OG-netizen/Project-3-4/Sprint Planning/Scrum meeting 3.pptx

## PO Meeting

## Sprint review

- Nieuwe database
- Kleuren

## oude Presentatie Sprint Backlog

Features | Wat | Wie | Waarom | Taken | Moeilijkheids-graad | Acceptance criteria
4 | Bon laten printen. | De klant | Zodat je jouw transactie kan bekijken. | Fritzing van de bonprinter | 6 | De printer moet een bon kunnen printen met gekozen tekst
| | | | Code schrijven voor printer
5 | Kan zijn of haar saldo checken. | De klant | Zodat de klant overzicht heeft op zijn bank | Test database maken | 10 | De database moet een connectie hebben met de rest van de programma’s
| | | | Java > SQL

## Slide 4

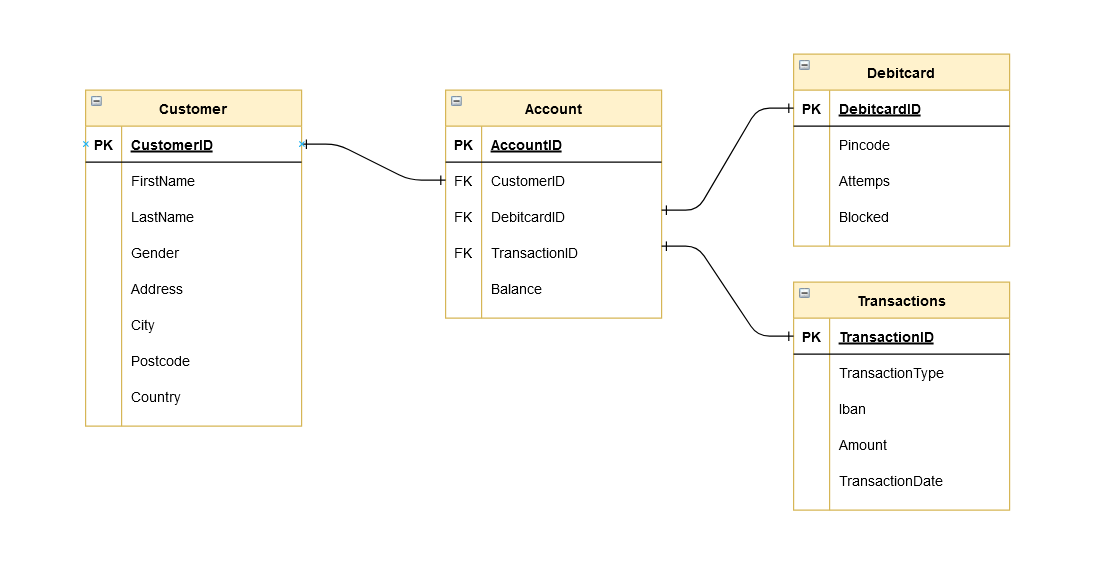
[picture p15: figure]

## kleuren

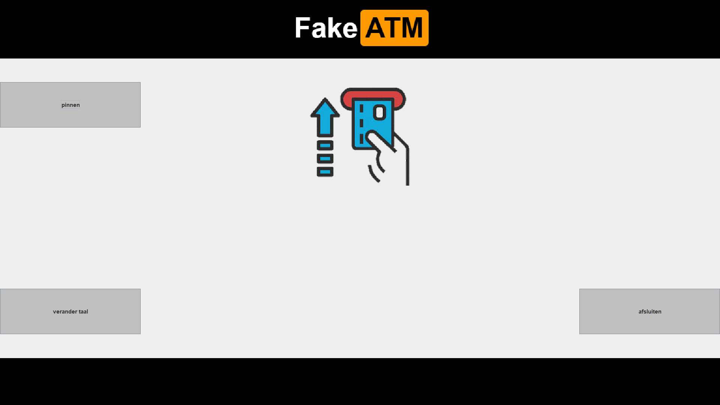
[picture p16: figure]

## Nieuwe Presentatie Sprint Backlog

Features | Wat | Wie | Waarom | Taken | Moeilijkheids-graad | Acceptance criteria
6 | Ontwerp om biljetten te behouden en weggeven. | De klant | Zodat de klant zijn biljetten kan opnemen. | Biljetten ontwerpen | 10 | Het geld dispenser moet biljetten uitwerpen.
| | | | Afmetingen gelddispenser | | Het IR sensor moet per biljet het waarde opnemen.
| | | | Ontwerpen gelddispenser | | Ontwerp van de gelddispenser moet 3 biljet soorten bewaren.
| | | | Afmetingen IR sensoren

## Retrospective
