OG-netizen/Project-3-4/Documenten/Aantekeningen Sprint/Sprint 3.docx

Geslacht nodig om op te slaan??

Niet nodig.

Doelgroep overleg over ontwerp va de GUI (Lettertype kleuren grootte etc.)

Grootere text, hoe bedienen

Vraag doelgroep!

IR Sensor om waarde? Beter aantal

Dingen worden gezegd die er niet staan (moeilijkheid 10)

Leg meer uit leganda of zo iets

Iets te veel voor 1 userstory.

5 10 en20, maarkanje ook 5 euro biljetten ipinnen, misschien handiger voor 10 20 en 50.

Meer vragen aan PO, voorstellen met “onderzoek” en dan vragen precies welke.

Aangepast maar niet laten zien.

Papier schud door de lucht. Hoe checken met IR.

Goed langs de IR laten gaan.

Taakverdeling voor Dia’s bedenken.

Tekst GUI groter.

GUI met database?

Niet handig, (API gebruiken!)

Bryan stond met rug naar daisy, erg gemeen.
