OG-netizen/Project-3-4/Documenten/Opdracht Risicolog.docx

Risicolog

Formuleer minimaal 6 risico’s

Risico | Impact (1 t/m 5) | Kans (1 t/m 5) | Hoe te voorkomen en hoe op te lossen.
Server niet bereikbaar | 4 | 2 | Melding maken bij de balie en doorgaan met een ander onderdeel.
Applicatie crash door bugs in broncode | 5 | 2 | Voorzichtiger programmeren, exception handler gebruiken zodat het niet onverwachts crasht.
Ongeautoriseerde toegang tot netwerk | 5 | 1 | Ons netwerk moet wel goed beveiligd zijn een firewall. Als die firewall niet genoeg is zullen wij remote Access VPN gebruiken datasnelheid door VPN is wel langzamer maar dat is niet belangrijk bij ons soort project waarbij veiligheid balngrijker is dan snelheid.
Plofkraak | 5 | 1 | Een security guard plaatsen, alarm en camera opzetten.
Een virus in onze atm software werd geinstalleerd. | 5 | 1 | secure programmeren. En virus scanner installeren op onze atm.
Servers wordt bereikt door iemand anders dan de ATM | 1 | 1 | De server alleen toegankelijk maken door de ATM door bijvoorbeeld een account in de server aan te maken.

1 = laag

5 = hoog

Geef als legenda een omschrijving van wat ‘laag’ en ‘hoog’ voor jullie betekent.

Groepsleden: Bryan Chung(0990458), Jurgen van Berg(1000875), JiaHacks(0992427), Wouter van Huut(1018984)
