OG-netizen/Project-3-4/User stories/UserStories.docx

Als klant wil ik me pas kunnen scannen om geld te pinnen

Als klant wil ik een algemene GUI zien om, te weten wat ik moet doen.

Als Klant wil ik een pincode om in te loggen. Zodat niet iedereen mijn geld kan pinnen.

Als klant wil ik een bon krijgen na het pinnen zodat ik zie wat is gepind.

Als Klant wil ik mijn saldo zien zodat ik weet hoeveel ik kan pinnen
