OG-netizen/Project-3-4/Documenten/Aantekeningen Sprint/sprint 5.docx

Aceptietietest // UNIT test maken

Elk onderdeel testen door te automatiseren

Week 7 les
