OG-netizen/Project-3-4/database/Inhoud van elke table/Account inhoud.png

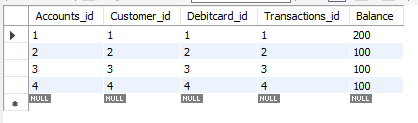
database/Inhoud van elke table/Account inhoud.png
