OG-netizen/Project-3-4/Documenten/Architectuur ontwerp/Architectuur ontwerp.png

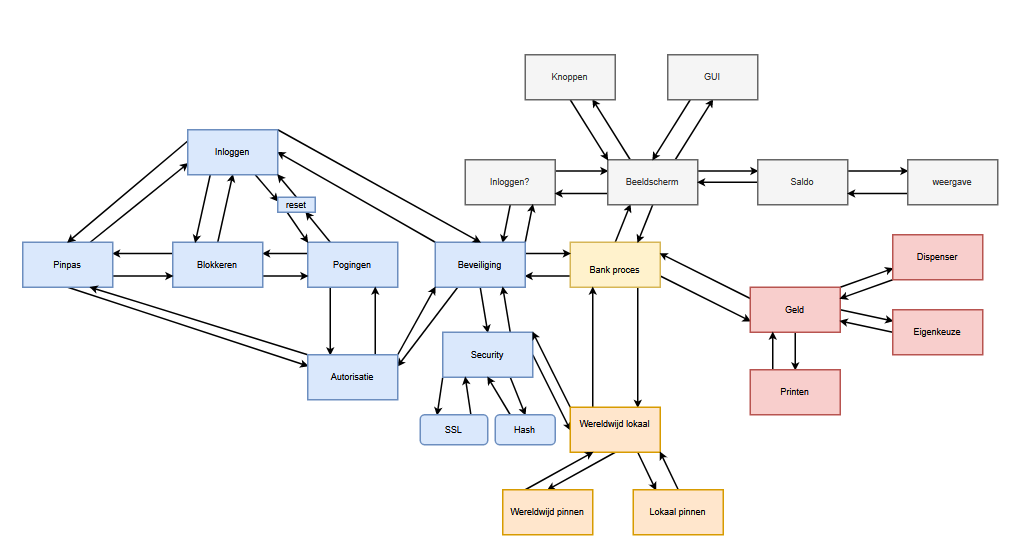
Documenten/Architectuur ontwerp/Architectuur ontwerp.png
