OG-netizen/Project-3-4/Documenten/Database ontwerp/database Accounts.png

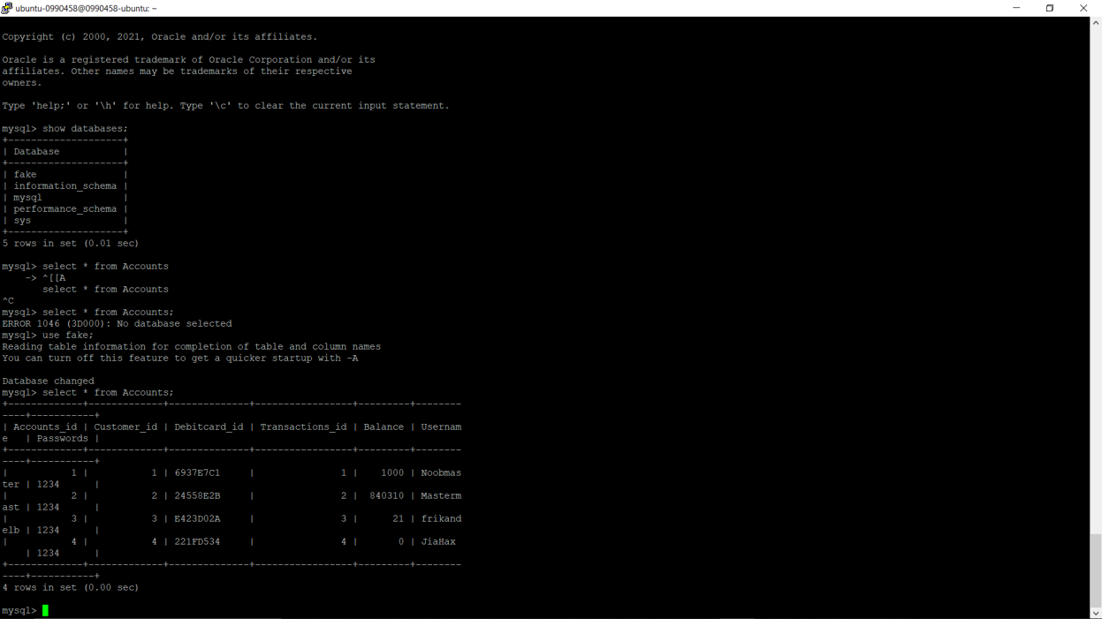
Documenten/Database ontwerp/database Accounts.png
