OG-netizen/Project-3-4/Documenten/Database ontwerp/database ontwerp 3.png

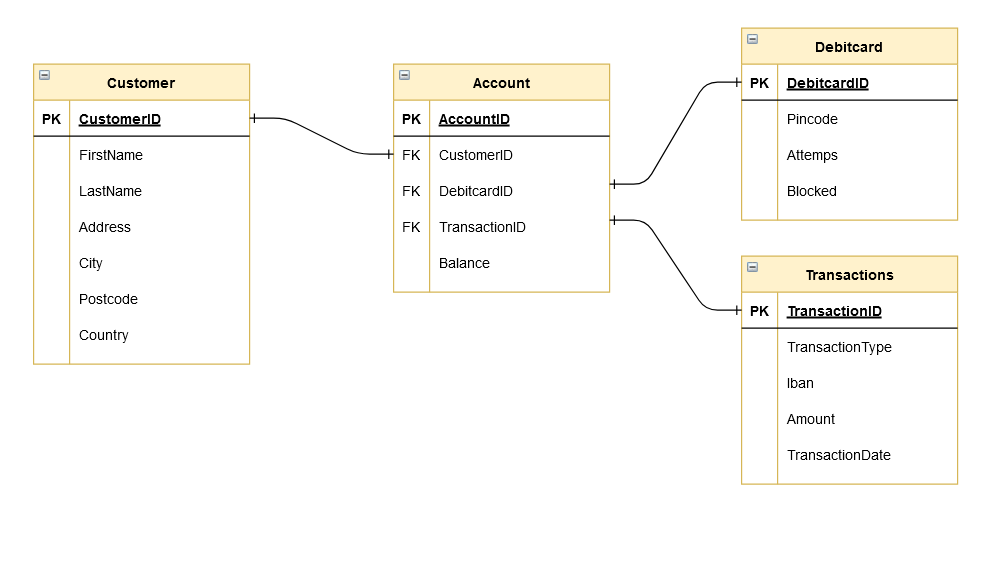
Documenten/Database ontwerp/database ontwerp 3.png
