OG-netizen/Project-3-4/Documenten/Schem. Ontwerp/Schematisch Ontwerp/Ontwerp.png

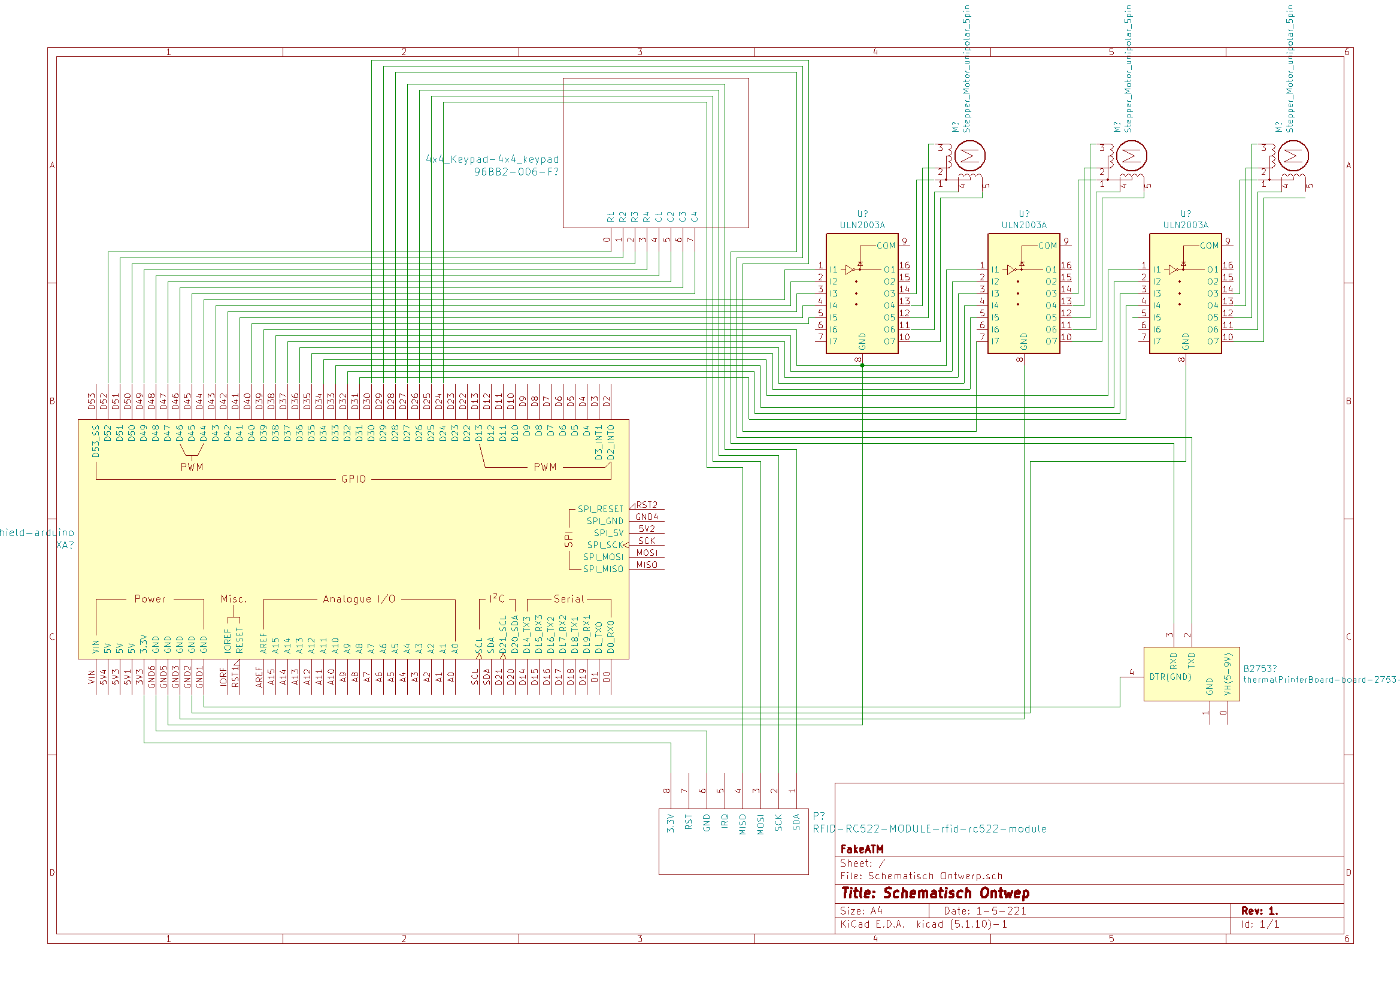
Documenten/Schem. Ontwerp/Schematisch Ontwerp/Ontwerp.png
