OG-netizen/Project-3-4/Documenten/Schema/Electrisch schema.png

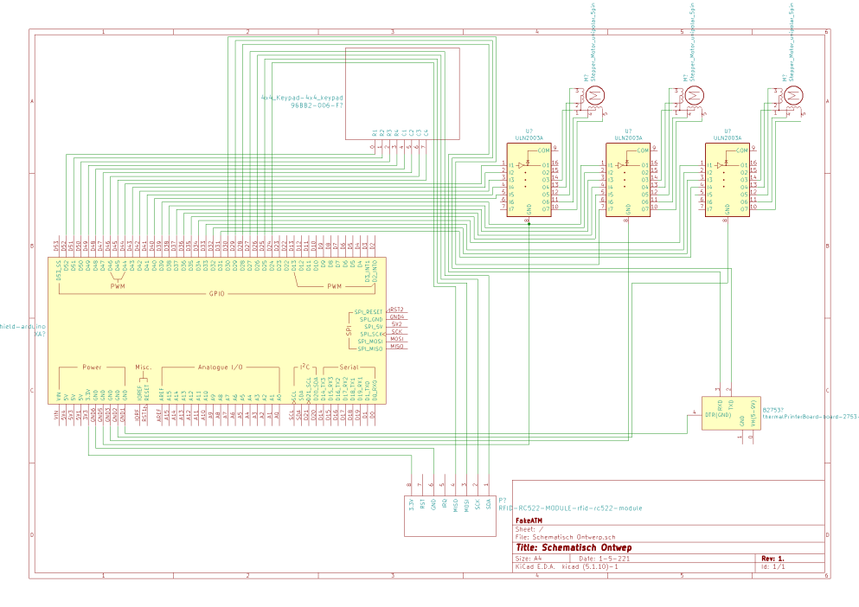
Documenten/Schema/Electrisch schema.png
