OG-netizen/Project-3-4/Documenten/site in.png

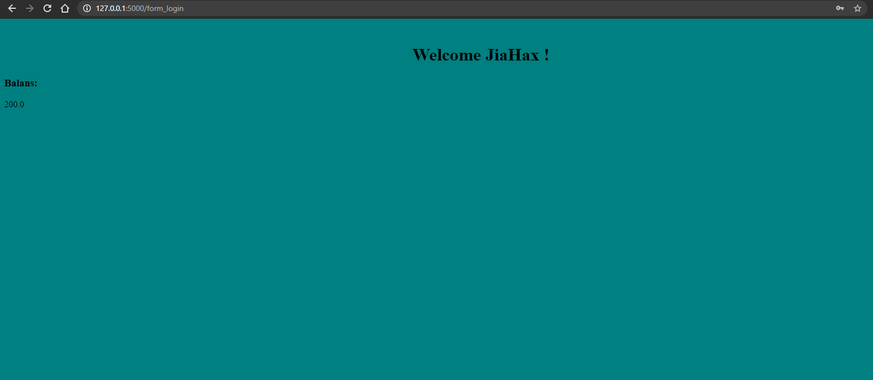
Documenten/site in.png
