OG-netizen/Project-3-4/code/Alles/Losse onderdelen/KeypadenRFID/KeypadenRFID/KeypadenRFID.ino

#include <SPI.h>
#include <MFRC522.h>
#include <Keypad.h>

#define RST_PIN         9           // Configurable, see typical pin layout above
#define SS_PIN          10          // Configurable, see typical pin layout above

const int ROW_NUM = 4; //four rows
const int COLUMN_NUM = 4; //four columns

char keyps[ROW_NUM][COLUMN_NUM] = {
  {'1','2','3', 'A'},
  {'4','5','6', 'B'},
  {'7','8','9', 'C'},
  {'*','0','#', 'D'}
};
string data[ROW][COLUMN] = {
{"79 2C E9 C1","1234"
};
byte pin_rows[ROW_NUM] = {9, 8, 7, 6}; //connect to the row pinouts of the keypad
byte pin_column[COLUMN_NUM] = {5, 4, 3, 2}; //connect to the column pinouts of the keypad

Keypad keypad = Keypad( makeKeymap(keyps), pin_rows, pin_column, ROW_NUM, COLUMN_NUM );
MFRC522 mfrc522(SS_PIN, RST_PIN);   // Create MFRC522 instance

//*****************************************************************************************//
void setup() {
  Serial.begin(9600);                                           // Initialize serial communications with the PC
  SPI.begin();                                                  // Init SPI bus
  mfrc522.PCD_Init();                                              // Init MFRC522 card
  Serial.println(F("Read personal data on a MIFARE PICC:"));    //shows in serial that it is ready to read
}

//*****************************************************************************************//
void loop() {

  //keypad--------------------------------------------------------
  
  char keyp = keypad.getKey();

  if (keyp){
    Serial.println(keyp);
  }
  else {
  //----------------------------------------------------------------------


  // Prepare key - all keys are set to FFFFFFFFFFFFh at chip delivery from the factory.
  MFRC522::MIFARE_Key key;
  for (byte i = 0; i < 6; i++) key.keyByte[i] = 0xFF;

  //some variables we need
  byte block;
  byte len;
  MFRC522::StatusCode status;

  //-------------------------------------------

  // Reset the loop if no new card present on the sensor/reader. This saves the entire process when idle.
  if ( ! mfrc522.PICC_IsNewCardPresent()) {
    return;
  }

  // Select one of the cards
  if ( ! mfrc522.PICC_ReadCardSerial()) {
    return;
  }

  Serial.println(F("**Card Detected:**"));

  //-------------------------------------------

  mfrc522.PICC_DumpDetailsToSerial(&(mfrc522.uid)); //dump some details about the card

  //mfrc522.PICC_DumpToSerial(&(mfrc522.uid));      //uncomment this to see all blocks in hex

  //-------------------------------------------

  Serial.print(F("Name: "));

  byte buffer1[18];

  block = 4;
  len = 18;

  //------------------------------------------- GET FIRST NAME
  status = mfrc522.PCD_Authenticate(MFRC522::PICC_CMD_MF_AUTH_KEY_A, 4, &key, &(mfrc522.uid)); //line 834 of MFRC522.cpp file
  if (status != MFRC522::STATUS_OK) {
    Serial.print(F("Authentication failed: "));
    Serial.println(mfrc522.GetStatusCodeName(status));
    return;
  }

  status = mfrc522.MIFARE_Read(block, buffer1, &len);
  if (status != MFRC522::STATUS_OK) {
    Serial.print(F("Reading failed: "));
    Serial.println(mfrc522.GetStatusCodeName(status));
    return;
  }

  //PRINT FIRST NAME
  for (uint8_t i = 0; i < 16; i++)
  {
    if (buffer1[i] != 32)
    {
      Serial.write(buffer1[i]);
    }
  }
  Serial.print(" ");

  //---------------------------------------- GET LAST NAME

  byte buffer2[18];
  block = 1;

  status = mfrc522.PCD_Authenticate(MFRC522::PICC_CMD_MF_AUTH_KEY_A, 1, &key, &(mfrc522.uid)); //line 834
  if (status != MFRC522::STATUS_OK) {
    Serial.print(F("Authentication failed: "));
    Serial.println(mfrc522.GetStatusCodeName(status));
    return;
  }

  status = mfrc522.MIFARE_Read(block, buffer2, &len);
  if (status != MFRC522::STATUS_OK) {
    Serial.print(F("Reading failed: "));
    Serial.println(mfrc522.GetStatusCodeName(status));
    return; 
  }

  //PRINT LAST NAME
  for (uint8_t i = 0; i < 16; i++) {
    Serial.write(buffer2[i] );
  }


  //----------------------------------------

  Serial.println(F("\n**End Reading**\n"));

  delay(1000); //change value if you want to read cards faster

  mfrc522.PICC_HaltA();
  mfrc522.PCD_StopCrypto1();
}
}
//*****************************************************************************************//
