OG-netizen/Project-3-4/code/Alles/Losse onderdelen/Motor/Motor.ino

#define A 2
#define B 3
#define C 4
#define D 5
 
#define NUMBER_OF_STEPS_PER_REV 512
int wacht = 1;

int i = 0;

void setup(){
pinMode(A,OUTPUT);
pinMode(B,OUTPUT);
pinMode(C,OUTPUT);
pinMode(D,OUTPUT);
}

void write(int a,int b,int c,int d){
digitalWrite(A,a);
digitalWrite(B,b);
digitalWrite(C,c);
digitalWrite(D,d);
}

void onestep(){
write(1,0,0,0);
delay(wacht);
write(1,1,0,0);
delay(wacht);
write(0,1,0,0);
delay(wacht);
write(0,1,1,0);
delay(wacht);
write(0,0,1,0);
delay(wacht);
write(0,0,1,1);
delay(wacht);
write(0,0,0,1);
delay(wacht);
write(1,0,0,1);
delay(wacht);
}

void reverse(){
write(1,0,0,1);
delay(wacht);
write(0,0,0,1);
delay(wacht);
write(0,0,1,1);
delay(wacht);
write(0,0,1,0);
delay(wacht);
write(0,1,1,0);
delay(wacht);
write(0,1,0,0);
delay(wacht);
write(1,1,0,0);
delay(wacht);
write(1,0,0,0);
delay(wacht);
}

void loop(){
while(i<NUMBER_OF_STEPS_PER_REV){
reverse();
i++;
}
}
